BSidesFortWayne/BSidesFW2025Badge/src/apps/battery_monitor.py

from apps.app import BaseApp
import framebuf
from lib.microfont import MicroFont
import gc9a01

class BatteryMonitor(BaseApp):
    name = "Battery Monitor"
    version = "0.0.3"
    def __init__(self, controller):
        super().__init__(controller)
        self.display1 = self.controller.bsp.displays.display1

        self.bg_color = gc9a01.WHITE
        self.fg_color = gc9a01.BLACK
        
        self.font = MicroFont("fonts/victor_R_24.mfnt", cache_index=True, cache_chars=True)

        self.controller.bsp.displays.display_center_text("Battery")

        self.display2_mem_buf = bytearray(240*240*2)
        self.display2_fbuf_mv = memoryview(self.display2_mem_buf)
        self.display2_fbuf = framebuf.FrameBuffer(
            self.display2_mem_buf, 
            240, 
            240, 
            framebuf.RGB565
        )

        self.center = self.display1.width() // 2

    def draw_voltage_meter(self):
        # print(f'{raw}raw, {mv}mv')
        # self.raw_average.add(raw)

        self.display2_fbuf.fill(gc9a01.BLACK)

        off_x, off_y = self.font.write(
            f'Voltage: {self.controller.battery.mv_average.average()}mv',
            self.display2_fbuf_mv,
            framebuf.RGB565,
            240,
            240,
            5,
            120,
            gc9a01.WHITE
        )

        off_x, off_y = self.font.write(
            f'Battery: {self.controller.battery.get_battery_percentage()}%',
            self.display2_fbuf_mv,
            framebuf.RGB565,
            240,
            240,
            5,
            120 - off_y,
            gc9a01.WHITE
        )

    async def update(self):
        self.draw_voltage_meter()
        self.controller.battery.draw_battery(self.controller.displays.display1, (120-15, 240-60))
        self.controller.displays.display2.blit_buffer(self.display2_fbuf_mv, 0, 0, 240, 240)

if __name__ == "__main__":
    from single_app_runner import run_app
    run_app(BatteryMonitor, perf=True)
