BSidesFortWayne/BSidesFW2025Badge/src/apps/view0.py

import asyncio
import gc9a01
from apps.app import BaseApp
import fonts.arial32px as arial32px
from lib.microfont import MicroFont
import framebuf

class App(BaseApp):
    """
    Displays name on both screens.
    The buttons go to the other 4 views.
    """
    name = "Badge"
    def __init__(self, controller):
        super().__init__(controller)
        self.view = 0
        self.displays = self.controller.bsp.displays

        # define colors
        self.black = self.displays.COLOR_LOOKUP['gc9a01']['black']
        self.white = self.displays.COLOR_LOOKUP['gc9a01']['white']
        self.red = self.displays.COLOR_LOOKUP['gc9a01']['red']
        self.blue = self.displays.COLOR_LOOKUP['gc9a01']['blue']
        self.magenta = self.displays.COLOR_LOOKUP['gc9a01']['magenta']
        self.yellow = self.displays.COLOR_LOOKUP['gc9a01']['yellow']
        self.cyan = self.displays.COLOR_LOOKUP['gc9a01']['cyan']
        self.green = self.displays.COLOR_LOOKUP['gc9a01']['green']

        self.config.add('first_name', 'WhatAbout')
        self.config.add('last_name', 'Bob')
        self.config.add('company', 'BSidesFW')
        self.config.add('title', '2025')
        self.config.add('background_image', "img/bsides_logo.jpg")
        self.config.add('bg_color_index', 0)
        self.config.add('fg_color_index', 1)

        self.showing_time = False
        self.switch_to_badge = False

        self.last_checksum = self.config.checksum()
        self.color_options = [self.black, self.white, self.red, self.blue, self.magenta, self.yellow, self.cyan, self.green]

        # framebuffer for showing time
        self.fbuf_width = 200
        self.fbuf_height = 240

        self.fbuf_mem = bytearray(self.fbuf_width*self.fbuf_height*2)
        self.fbuf = framebuf.FrameBuffer(
            self.fbuf_mem, 
            self.fbuf_width, 
            self.fbuf_height, 
            framebuf.RGB565
        )
        self.fbuf_mv = memoryview(self.fbuf_mem)
        self.font = MicroFont("fonts/victor_B_32.mfnt", cache_index=True, cache_chars=True)

    def wrap_text(self, text, font, max_width, display):
        words = text.split(' ')
        lines = []
        current_line = ''

        for word in words:
            if display.write_len(font, current_line + word + ' ') <= max_width:
                current_line += word + ' '
            else:
                lines.append(current_line.strip())
                current_line = word + ' '
        if current_line:
            lines.append(current_line.strip())
        return lines

    async def setup(self):
        first_name = self.config['first_name']
        last_name = self.config['last_name']
        company = self.config['company']
        title = self.config['title']
        bg_color_index = self.config['bg_color_index']
        fg_color_index = self.config['fg_color_index']

        if not first_name and not last_name:
            self.displays.display_center_text(
                'NO',
                self.white,
                self.black,
                1,
                arial32px
            )
            self.displays.display_center_text(
                'NAME',
                self.white,
                self.black,
                2,
                arial32px
            )
        else:
            # Convert hex to RGB
            display1_fg_color = self.color_options[fg_color_index]
            display2_fg_color = self.color_options[fg_color_index]
            display1_bg_color = self.color_options[bg_color_index]
            display2_bg_color = self.color_options[bg_color_index]

            self.displays.display1.fill(display1_bg_color)
            self.displays.display2.fill(display2_bg_color)

            max_width = self.displays.display1.width() - 40  # Adjust padding as needed
            wrapped_first_name = self.wrap_text(first_name, arial32px, max_width, self.displays.display1)
            wrapped_last_name = self.wrap_text(last_name, arial32px, max_width, self.displays.display1)
            wrapped_company = self.wrap_text(company, arial32px, max_width, self.displays.display2)
            wrapped_title = self.wrap_text(title, arial32px, max_width, self.displays.display2)

            # Debugging information
            print("Wrapped First Name:", wrapped_first_name)
            print("Wrapped Last Name:", wrapped_last_name)
            print("Wrapped Company:", wrapped_company)
            print("Wrapped Title:", wrapped_title)

            # Calculate total height of the wrapped text
            total_height_first_name = len(wrapped_first_name) * arial32px.HEIGHT
            total_height_last_name = len(wrapped_last_name) * arial32px.HEIGHT
            total_height_company = len(wrapped_company) * arial32px.HEIGHT
            total_height_title = len(wrapped_title) * arial32px.HEIGHT

            # Move vertical alignment up by X pixels
            adjustment = 10

            # Calculate y-offset to center the text vertically
            y_offset_first_name = (self.displays.display1.height() - total_height_first_name) // 2 - adjustment
            y_offset_last_name = (self.displays.display1.height() - total_height_last_name) // 2 - adjustment
            y_offset_company = (self.displays.display2.height() - total_height_company) // 2 - adjustment
            y_offset_title = (self.displays.display2.height() - total_height_title) // 2 - adjustment

            # Render first name and last name on display1
            for i, line in enumerate(wrapped_first_name):
                self.displays.display1.write(
                    arial32px,
                    line,
                    int((self.displays.display1.width() / 2) - (self.displays.display1.write_len(arial32px, line) / 2)),
                    y_offset_first_name + i * arial32px.HEIGHT,
                    display1_fg_color,
                    display1_bg_color
                )

            for i, line in enumerate(wrapped_last_name):
                self.displays.display1.write(
                    arial32px,
                    line,
                    int((self.displays.display1.width() / 2) - (self.displays.display1.write_len(arial32px, line) / 2)),
                    y_offset_last_name + i * arial32px.HEIGHT + total_height_first_name,
                    display1_fg_color,
                    display1_bg_color
                )

            # Render company and title on display2
            for i, line in enumerate(wrapped_company):
                self.displays.display2.write(
                    arial32px,
                    line,
                    int((self.displays.display2.width() / 2) - (self.displays.display2.write_len(arial32px, line) / 2)),
                    y_offset_company + i * arial32px.HEIGHT,
                    display2_fg_color,
                    display2_bg_color
                )

            for i, line in enumerate(wrapped_title):
                self.displays.display2.write(
                    arial32px,
                    line,
                    int((self.displays.display2.width() / 2) - (self.displays.display2.write_len(arial32px, line) / 2)),
                    y_offset_title + i * arial32px.HEIGHT + total_height_company,
                    display2_fg_color,
                    display2_bg_color
                )

    async def update(self):
        if self.showing_time:
            self.update_time()
            if self.switch_to_badge:
                self.showing_time = False
                self.switch_to_badge = False
                await self.setup()
        else:
            if self.config.checksum() != self.last_checksum:
                await self.setup()
                self.last_checksum = self.config.checksum()
            await asyncio.sleep(3)

    async def handle_button_press(self, button):
        image = self.config['background_image']
        if button == 0:
            self.displays[1].jpg(image, 0, 0, gc9a01.FAST)
        elif button == 4:
            # Update background color
            self.config['bg_color_index'] = (self.config['bg_color_index'] + 1) % len(self.color_options)
            self.displays.display2.fill(self.color_options[self.config['bg_color_index']])
        elif button == 5:
            # Update font color
            self.config['fg_color_index'] = (self.config['fg_color_index'] - 1) % len(self.color_options)
            self.displays.display2.fill(self.color_options[self.config['fg_color_index']])

    def button_press(self, button):
        print(button)
        if button == 6:
            self.controller.bsp.displays.display1.fill(gc9a01.BLACK)
            self.controller.bsp.displays.display2.fill(gc9a01.BLACK)
            self.update_time()
            self.showing_time = True
        else:
            asyncio.create_task(self.handle_button_press(button))

    def button_click(self, button):
        pass

    def update_time(self):
        time_now = self.controller.bsp.rtc.datetime()

        self.fbuf.fill(gc9a01.BLACK)

        off_x, off_y = self.font.write(
            '{:02}:{:02}'.format(time_now[4], time_now[5]),
            self.fbuf_mv,
            framebuf.RGB565,
            self.fbuf_width,
            self.fbuf_height,
            int(self.fbuf_width/2)-30,
            int(self.fbuf_height/2)-int(self.font.height/2),
            gc9a01.WHITE
        )

        self.controller.bsp.displays.display1.blit_buffer(
            self.fbuf_mv,
            0,
            0,
            self.fbuf_width,
            self.fbuf_height
        )
 
    def button_release(self, button):
        if button == 6:
            self.switch_to_badge = True

    def button_long_press(self, button):
        pass
