BSidesFortWayne/BSidesFW2025Badge/src/apps/view3.py

import apps.app

class App(apps.app.BaseApp):
    name = "Blue View"
    def __init__(self, controller: apps.app.IController):
        super().__init__(controller)
        displays = self.controller.bsp.displays
        blue = displays.COLOR_LOOKUP['gc9a01']['blue']
        displays.display1.fill(blue)
        displays.display2.fill(blue)
