BSidesFortWayne/BSidesFW2025Badge/src/apps/view.py

class View:
    def __init__(self):
        super().__init__()

    def update(self):
        """
        Is called every 50 milliseconds.
        """
        
        pass
    
    def button_press(self, button):
        """
        Called when a button is pressed.
        """

        pass
